nuniesmith/otr620/src/stl/v0.2/otr620_shelf.stl

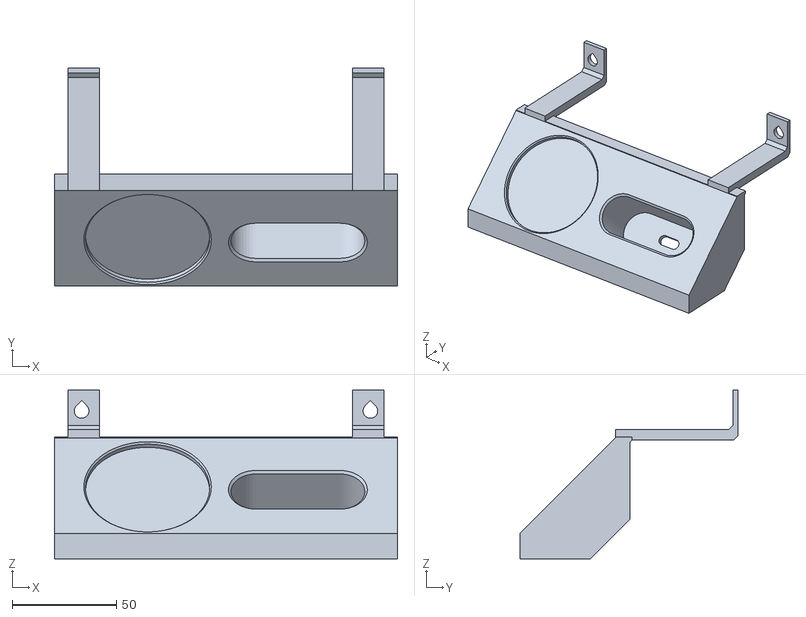
[picture p17: CAD file, 2026-09-17, an earlier design]
src/stl/v0.2/otr620_shelf.stl
164.5 x 104.6 x 81.0
