nuniesmith/otr620/src/stl/v0.2/fit_test_1_face_frame.stl

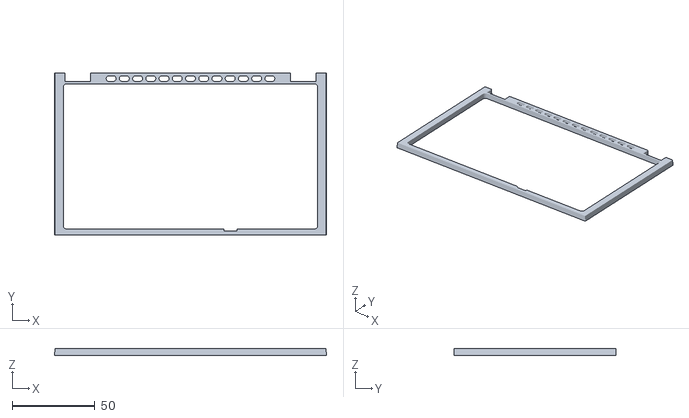
[picture p18: CAD file, 2026-09-17, an earlier design]
src/stl/v0.2/fit_test_1_face_frame.stl
164.5 x 98.0 x 4.00
